Xinyuan-LilyGO/T-Display-S3-Pro/examples/factory/factory.ino

#include <SensorLTR553.hpp>
#include <Wire.h>
#include <WiFi.h>
#include <esp_sntp.h>
#include <XPowersLib.h>
#include "LV_Helper.h"
#include "ui.h"
#include "utilities.h"
#include <esp_camera.h>
#include "ESP32_OV5640_AF.h"
#include "sd_card.h"
#include "EEPROM.h"
/*********************************************************************************
 *                               EEPROM
 *********************************************************************************/
#define EEPROM_SIZE_MAX 5
#define EEPROM_MAGIC_NUM 0xAA
#define EEPROM_FRIST_ADDR  0
#define EEPROM_CAMERA_ADDR 1
uint8_t eeprom_buf[EEPROM_SIZE_MAX];

extern bool camera_rotation_flag;
/*********************************************************************************
 *                              TYPEDEFS
 *********************************************************************************/
static SensorLTR553 als;
static PowersSY6970 PMU;
static WiFiEvent_t event;
static QueueHandle_t wifi_setting_queue;
static EventGroupHandle_t touch_eg;
static bool hasSensor = false, hasPMU = false;
static int autonBrightness = 0;

void eeprom_write(int addr, uint8_t val)
{
    eeprom_buf[EEPROM_FRIST_ADDR] = EEPROM_MAGIC_NUM;
    eeprom_buf[addr] = val;

    for(int i = 0; i < EEPROM_SIZE_MAX; i++){
        EEPROM.write(i, eeprom_buf[i]);
    }
    EEPROM.commit();
    for (int i = 0; i < EEPROM_SIZE_MAX; i++) {
        Serial.print(byte(EEPROM.read(i))); Serial.print(" ");
    }
    Serial.println("");
}

void eeproom_init(void)
{
    if (!EEPROM.begin(EEPROM_SIZE_MAX)) {
        Serial.println("failed to initialise EEPROM"); delay(1000000);
    }
    Serial.println(" bytes read from Flash . Values are:");

    for (int i = 0; i < EEPROM_SIZE_MAX; i++) {
        eeprom_buf[i] = EEPROM.read(i);
        Serial.print(byte(EEPROM.read(i))); Serial.print(" ");
    }

    uint8_t frist_read = eeprom_buf[EEPROM_FRIST_ADDR];
    Serial.printf(" read = %d\n", frist_read);
    if(frist_read == EEPROM_MAGIC_NUM){
        camera_rotation_flag = eeprom_buf[EEPROM_CAMERA_ADDR];
    }else{
        lv_memset_00(eeprom_buf, EEPROM_SIZE_MAX);
        for(int i=0; i < EEPROM_SIZE_MAX; i++){
            EEPROM.write(i, eeprom_buf[i]);
        }
        EEPROM.commit();
    }
}

void lv_auto_brightne_cd(void)
{
    if (!hasSensor)return;
    autonBrightness = autonBrightness == 0 ? 1 : 0;
}

void WiFiEvent(WiFiEvent_t event)
{
    switch (event) {
    case ARDUINO_EVENT_WIFI_READY:
        Serial.println("WiFi interface ready");
        break;
    case ARDUINO_EVENT_WIFI_SCAN_DONE:
        Serial.println("Completed scan for access points");
        break;
    case ARDUINO_EVENT_WIFI_STA_START:
        Serial.println("WiFi client started");
        break;
    case ARDUINO_EVENT_WIFI_STA_STOP:
        Serial.println("WiFi clients stopped");
        break;
    case ARDUINO_EVENT_WIFI_STA_CONNECTED:
        //xQueueSend(wifi_setting_queue, &event, 0);
        Serial.println("Connected to access point");
        break;
    case ARDUINO_EVENT_WIFI_STA_DISCONNECTED:
        xQueueSend(wifi_setting_queue, &event, 0);
        Serial.println("Disconnected from WiFi access point");
        break;
    case ARDUINO_EVENT_WIFI_STA_AUTHMODE_CHANGE:
        Serial.println("Authentication mode of access point has changed");
        break;
    case ARDUINO_EVENT_WIFI_STA_GOT_IP:
        xQueueSend(wifi_setting_queue, &event, 0);
        Serial.print("Obtained IP address: ");
        Serial.println(WiFi.localIP());
        break;
    case ARDUINO_EVENT_WIFI_STA_LOST_IP:
        Serial.println("Lost IP address and IP address is reset to 0");
        break;
    default: break;
    }
}

bool initSensor()
{

    if (!als.begin(Wire, LTR553_SLAVE_ADDRESS, BOARD_I2C_SDA, BOARD_I2C_SCL)) {
        Serial.println("Failed to find LTR553 - check your wiring!");
        return false;
    }

    Serial.println("Init LTR553 Sensor success!");

    // Set the ambient light high and low thresholds.
    // If the value exceeds or falls below the set value, an interrupt will be triggered.
    als.setLightSensorThreshold(10, 200);

    // Set the high and low thresholds of the proximity sensor.
    // If the value exceeds or falls below the set value, an interrupt will be triggered.
    // als.setProximityThreshold(10, 30);

    // Controls the Light Sensor N number of times the measurement data is outside the range
    // defined by the upper and lower threshold limits before asserting the interrupt.
    als.setLightSensorPersists(1);

    // Controls the Proximity  N number of times the measurement data is outside the range
    // defined by the upper and lower threshold limits before asserting the interrupt.
    als.setProximityPersists(1);

    /*
    *  ALS_IRQ_ACTIVE_LOW, // INT pin is considered active when it is a logic 0 (default)
    *  ALS_IRQ_ACTIVE_HIGH // INT pin is considered active when it is a logic 1
    * * */
    als.setIRQLevel(SensorLTR553::ALS_IRQ_ACTIVE_LOW);

    /*
    *  ALS_IRQ_ONLY_PS,    // Only PS measurement can trigger interrupt
    *  ALS_IRQ_ONLY_ALS,   // Only ALS measurement can trigger interrupt
    *  ALS_IRQ_BOTH,       // Both ALS and PS measurement can trigger interrupt
    * * * */
    als.enableIRQ(SensorLTR553::ALS_IRQ_BOTH);

    /*
    *   ALS_GAIN_1X  ,   -> 1 lux to 64k lux (default)
    *   ALS_GAIN_2X  ,   -> 0.5 lux to 32k lux
    *   ALS_GAIN_4X  ,   -> 0.25 lux to 16k lux
    *   ALS_GAIN_8X  ,   -> 0.125 lux to 8k lux
    *   ALS_GAIN_48X ,   -> 0.02 lux to 1.3k lux
    *   ALS_GAIN_96X ,   -> 0.01 lux to 600 lux
    * */
    als.setLightSensorGain(SensorLTR553::ALS_GAIN_1X);

    /*
    *   PS_LED_PLUSE_30KHZ,
    *   PS_LED_PLUSE_40KHZ,
    *   PS_LED_PLUSE_50KHZ,
    *   PS_LED_PLUSE_60KHZ,
    *   PS_LED_PLUSE_70KHZ,
    *   PS_LED_PLUSE_80KHZ,
    *   PS_LED_PLUSE_90KHZ,
    *   PS_LED_PLUSE_100KHZ,
    * * * * * * * * * * */
    als.setPsLedPulsePeriod(SensorLTR553::PS_LED_PLUSE_100KHZ);


    /*
    *   PS_LED_DUTY_25,
    *   PS_LED_DUTY_50,
    *   PS_LED_DUTY_75,
    *   PS_LED_DUTY_100,
    * * * */
    als.setPsLedDutyCycle(SensorLTR553::PS_LED_DUTY_100);


    /*
    *   PS_LED_CUR_5MA,
    *   PS_LED_CUR_10MA,
    *   PS_LED_CUR_20MA,
    *   PS_LED_CUR_50MA,
    *   PS_LED_CUR_100MA,
    * * * * * * * */
    als.setPsLedCurrent(SensorLTR553::PS_LED_CUR_100MA);

    /*
    *   PS_MEAS_RATE_50MS,
    *   PS_MEAS_RATE_70MS,
    *   PS_MEAS_RATE_100MS,
    *   PS_MEAS_RATE_200MS,
    *   PS_MEAS_RATE_500MS,
    *   PS_MEAS_RATE_1000MS,
    *   PS_MEAS_RATE_2000MS,
    *   PS_MEAS_RATE_10MS
    * * * * * * * */
    als.setProximityRate(SensorLTR553::PS_MEAS_RATE_50MS);

    // Number of pulses
    als.setPsLedPulses(1);

    // Enable ambient light sensor
    als.enableLightSensor();

    // Enable proximity sensor
    als.enableProximity();

    // Enable proximity sensor saturation indication
    als.enablePsIndicator();
    return  true;
}

void updatePMU(lv_timer_t *t)
{
    if (!hasPMU)return;
    set_usbAndBattery(PMU.isVbusIn(), PMU.getVbusVoltage(), PMU.getBattVoltage());
}

void updateLightDected(lv_timer_t *t)
{
    int ps_thread = 40; // range: 0 ~ 100
    int ps_time = 2;    // 3 seconds to think there's an object covering the screen
    int ch0, ch1, ps;
    bool saturated = false;
    static uint32_t cnt = 0;
    static bool cover_flag = false;

    if (autonBrightness) {
        Serial.print(" ALS: CH1:"); Serial.print(als.getLightSensor(1));
        Serial.print(" -  CH0:"); Serial.print(als.getLightSensor(0));
        Serial.print(" -  PS:"); Serial.print(als.getProximity(&saturated));
        Serial.print(" -  "); Serial.println(saturated ? "PS saturated" : "PS not saturated");

        if (!hasSensor)
        return;

        ch0 = als.getLightSensor(0);
        ch1 = als.getLightSensor(1);
        ps = als.getProximity(&saturated);

        if(ps > ps_thread){
            if(!cover_flag){
                cnt++;
                if(cnt * t->period > ps_time * 1000){
                    digitalWrite(BOARD_TFT_BL, 0);
                    delay(3);
                    cnt = 0;
                    cover_flag = true;
                }
            }
        } else {
            if(cover_flag){
                cnt++;
                if(cnt * t->period > ps_time * 1000){
                    digitalWrite(BOARD_TFT_BL, 1);
                    delay(3);
                    cnt = 0;
                    cover_flag = false;
                }
            }else{
                cnt = 0;
            }
        }
    }
}

camera_config_t config;
OV5640 ov5640 = OV5640();
void camera_init(void)
{
    config.ledc_channel = LEDC_CHANNEL_0;
    config.ledc_timer = LEDC_TIMER_0;
    config.pin_d0 = CAMERA_PIN_Y2;
    config.pin_d1 = CAMERA_PIN_Y3;
    config.pin_d2 = CAMERA_PIN_Y4;
    config.pin_d3 = CAMERA_PIN_Y5;
    config.pin_d4 = CAMERA_PIN_Y6;
    config.pin_d5 = CAMERA_PIN_Y7;
    config.pin_d6 = CAMERA_PIN_Y8;
    config.pin_d7 = CAMERA_PIN_Y9;
    config.pin_xclk = CAMERA_PIN_XCLK;
    config.pin_pclk = CAMERA_PIN_PCLK;
    config.pin_vsync = CAMERA_PIN_VSYNC;
    config.pin_href = CAMERA_PIN_HREF;
    config.pin_sccb_sda = CAMERA_PIN_SIOD;
    config.pin_sccb_scl = CAMERA_PIN_SIOC;
    config.pin_pwdn = CAMERA_PIN_PWDN;
    config.pin_reset = CAMERA_PIN_RESET;
    config.xclk_freq_hz = XCLK_FREQ_HZ;
#if UI_CAMERA_CANVAS 
    config.pixel_format = PIXFORMAT_RGB565;
    config.frame_size = FRAMESIZE_240X240;
    config.jpeg_quality = 10;
    config.fb_count = 1;
#else
    config.pixel_format = PIXFORMAT_JPEG;
    config.frame_size = FRAMESIZE_HQVGA;
    config.jpeg_quality = 15;
    config.fb_count = 1;
#endif
    config.fb_location = CAMERA_FB_IN_PSRAM;
    config.grab_mode = CAMERA_GRAB_WHEN_EMPTY;

    esp_err_t err = esp_camera_init(&config);
    if (err != ESP_OK) {
        Serial.println("camera init error!");
    }
    sensor_t *s = esp_camera_sensor_get();

    if (s) {
        Serial.print("camera id:");
        Serial.println(s->id.PID);
        camera_sensor_info_t *sinfo = esp_camera_sensor_get_info(&(s->id));
        if (sinfo) {
            Serial.print("camera model:");
            Serial.println(sinfo->name);
        }
        if (s->id.PID == GC0308_PID) {
            s->set_vflip(s, 0); // This can't flip the picture vertically. Watch out!
            s->set_hmirror(s, 0);
        }else if (s->id.PID == OV5640_PID){
            ov5640.start(s);
            if (ov5640.focusInit() == 0) {
                Serial.println("OV5640_Focus_Init Successful!");
            }

            if (ov5640.autoFocusMode() == 0) {
                Serial.println("OV5640_Auto_Focus Successful!");
            }
            s->set_vflip(s, 1);
            s->set_hmirror(s, 0);
        }
    }

    // Initialize Camera LED
    // Adjust the LED duty cycle to save power and heat.
    // If you directly set the LED to HIGH, the heat brought by the LED will be huge,
    // and the current consumption will also be huge.
    ledcSetup(LEDC_WHITE_CH, 1000, 8);
    ledcAttachPin(CAMERA_WHITH_LED, LEDC_WHITE_CH);
    ledcWrite(LEDC_WHITE_CH, 0);
    // ledcWrite(LEDC_WHITE_CH, 20);
}


void setup()
{
    touch_eg = xEventGroupCreate();
    wifi_setting_queue = xQueueCreate(5, sizeof(uint16_t));

    Serial.begin(115200);

    eeproom_init();

    // vibrating motor init
    pinMode(VIBRATING_MOTOR, OUTPUT);
    digitalWrite(VIBRATING_MOTOR, LOW);

    WiFi.disconnect(true);
    WiFi.onEvent(WiFiEvent);

    const char *ntpServer1 = "pool.ntp.org";
    const char *ntpServer2 = "time.nist.gov";
    const char *tz  = "CST-8";                  //timezone
    configTzTime(tz, ntpServer1, ntpServer2);

    camera_init();

    hasPMU =  PMU.init(Wire, BOARD_I2C_SDA, BOARD_I2C_SCL, SY6970_SLAVE_ADDRESS);
    if (!hasPMU) {
        Serial.println("PMU is not online...");
    } else {
        PMU.disableOTG();
        PMU.enableADCMeasure();
        PMU.enableCharge();
    }

    hasSensor = initSensor();

    lv_helper();

    sd_card_init();

    lv_touch_homekey_set_cb(return_home_cd);

    ui_init();

    lv_timer_create(updatePMU, 1000, NULL);

    // TODO:
    lv_timer_create(updateLightDected, 500, NULL);
}

void loop()
{
    if (xQueueReceive(wifi_setting_queue, &event, 0)) {
        if (event == ARDUINO_EVENT_WIFI_STA_GOT_IP
                || event == ARDUINO_EVENT_WIFI_STA_DISCONNECTED) {
            wifi_connect_cd();
        }
    }
    lv_task_handler();
    delay(2);

}
