Xinyuan-LilyGO/T-Display-S3-Pro/examples/BHI260AP_Sensor/BHI260AP_Sensor.ino

/**
 *
 * @license MIT License
 *
 * Copyright (c) 2023 lewis he
 *
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
 * @file      BHI260AP_6DoF.ino
 * @author    Lewis He (lewishe@outlook.com)
 * @date      2023-09-06
 * @note      Changed from Boschsensortec API https://github.com/boschsensortec/BHY2_SensorAPI
 */
#include <Wire.h>
#include <SPI.h>
#include <Arduino.h>
#include "SensorBHI260AP.hpp"

#define SENSOR_SDA                  5
#define SENSOR_SCL                  6
#define SENSOR_IRQ                  21
#define SENSOR_RST                  -1

SensorBHI260AP bhy;

void accel_process_callback(uint8_t sensor_id, uint8_t *data_ptr, uint32_t len, uint64_t *timestamp)
{
    struct bhy2_data_xyz data;
    float scaling_factor = get_sensor_default_scaling(sensor_id);
    bhy2_parse_xyz(data_ptr, &data);
    Serial.print(bhy.getSensorName(sensor_id));
    Serial.print(":");
    Serial.printf("x: %f, y: %f, z: %f;\r\n",
                  data.x * scaling_factor,
                  data.y * scaling_factor,
                  data.z * scaling_factor
                 );
}


void gyro_process_callback(uint8_t sensor_id, uint8_t *data_ptr, uint32_t len, uint64_t *timestamp)
{
    struct bhy2_data_xyz data;
    float scaling_factor = get_sensor_default_scaling(sensor_id);
    bhy2_parse_xyz(data_ptr, &data);
    Serial.print(bhy.getSensorName(sensor_id));
    Serial.print(":");
    Serial.printf("x: %f, y: %f, z: %f;\r\n",
                  data.x * scaling_factor,
                  data.y * scaling_factor,
                  data.z * scaling_factor
                 );
}

void setup()
{
    Serial.begin(115200);
    while (!Serial);

    // Set the reset pin and interrupt pin, if any
    bhy.setPins(SENSOR_RST, SENSOR_IRQ);

    Serial.println("Initializing Sensors...");
    // Using I2C interface
    if (!bhy.init(Wire, SENSOR_SDA, SENSOR_SCL, BHI260AP_SLAVE_ADDRESS_L)) {
        Serial.print("Failed to initialize sensor - error code:");
        Serial.println(bhy.getError());
        while (1) {
            delay(1000);
        }
    }

    Serial.println("Initializing the sensor successfully!");

    // Output all available sensors to Serial
    bhy.printSensors(Serial);

    float sample_rate = 100.0;      /* Read out hintr_ctrl measured at 100Hz */
    uint32_t report_latency_ms = 0; /* Report immediately */

    // Enable acceleration
    bhy.configure(SENSOR_ID_ACC_PASS, sample_rate, report_latency_ms);
    // Enable gyroscope
    bhy.configure(SENSOR_ID_GYRO_PASS, sample_rate, report_latency_ms);

    // Set the acceleration sensor result callback function
    bhy.onResultEvent(SENSOR_ID_ACC_PASS, accel_process_callback);

    // Set the gyroscope sensor result callback function
    bhy.onResultEvent(SENSOR_ID_GYRO_PASS, gyro_process_callback);

}


void loop()
{
    // Update sensor fifo
    bhy.update();
    delay(50);
}
