Xinyuan-LilyGO/T-Display-S3-Pro/examples/PMU_Example/PMU_Example.ino

/**
 * @file      PMU_Example.ino
 * @author    Lewis He (lewishe@outlook.com)
 * @license   MIT
 * @copyright Copyright (c) 2023  Shenzhen Xin Yuan Electronic Technology Co., Ltd
 * @date      2023-09-25
 * @note      USB_CDC_ON_BOOT = Disable  , Messages are output from the QWIIC serial port
 */
#include <XPowersLib.h>
#include "utilities.h"


PowersSY6970 PMU;

uint32_t cycleInterval;

void setup()
{
    Serial.begin(115200);

    bool result = PMU.init(Wire, BOARD_I2C_SDA, BOARD_I2C_SCL, SY6970_SLAVE_ADDRESS);

    if (result == false) {
        while (1) {
            Serial.println("PMU is not online...");
            delay(50);
        }
    }
    // Set USB input current limit
    PMU.setInputCurrentLimit(1000);

    // The onboard battery is fully charged at 4.35V
    // Set the charging target voltage, Range:3840 ~ 4608mV ,step:16 mV
    PMU.setChargeTargetVoltage(4352);

    // Set the precharge current , Range: 64mA ~ 1024mA ,step:64mA
    PMU.setPrechargeCurr(64);

    // Set the charging current , Range:0~5056mA ,step:64mA
    PMU.setChargerConstantCurr(320);

    // When the battery is not connected and the USB is plugged in, the board's LED status indicator light will flash.
    // You can use `PMU.disableStatLed();` to turn off the indicator light,
    // but this means that if the battery is connected for charging, the LED light will also be disabled.
    // PMU.disableStatLed();

    // Enable charging led
    PMU.enableStatLed();

    // To obtain voltage data, the ADC must be enabled first
    PMU.enableADCMeasure();


    // For devices that have been connected to the battery, the charging function is turned on by default.
    // PMU.enableCharge();

    // For boards without an external battery, the charging function should be turned off, otherwise the power supply current of the power chip will be limited.
    PMU.disableCharge();

}



void loop()
{

    // SY6970 When VBUS is input, the battery voltage detection will not take effect
    if (millis() > cycleInterval) {

        Serial.println("Sats        VBUS    VBAT   SYS    VbusStatus      String   ChargeStatus     String      TargetVoltage       ChargeCurrent       Precharge       NTCStatus           String");
        Serial.println("            (mV)    (mV)   (mV)   (HEX)                         (HEX)                    (mV)                 (mA)                   (mA)           (HEX)           ");
        Serial.println("--------------------------------------------------------------------------------------------------------------------------------");
        Serial.print(PMU.isVbusIn() ? "Connected" : "Disconnect"); Serial.print("\t");
        Serial.print(PMU.getVbusVoltage()); Serial.print("\t");
        Serial.print(PMU.getBattVoltage()); Serial.print("\t");
        Serial.print(PMU.getSystemVoltage()); Serial.print("\t");
        Serial.print("0x");
        Serial.print(PMU.getBusStatus(), HEX); Serial.print("\t");
        Serial.print(PMU.getBusStatusString()); Serial.print("\t");
        Serial.print("0x");
        Serial.print(PMU.chargeStatus(), HEX); Serial.print("\t");
        Serial.print(PMU.getChargeStatusString()); Serial.print("\t");

        Serial.print(PMU.getChargeTargetVoltage()); Serial.print("\t");
        Serial.print(PMU.getChargerConstantCurr()); Serial.print("\t");
        Serial.print(PMU.getPrechargeCurr()); Serial.print("\t");
        Serial.print(PMU.getNTCStatus()); Serial.print("\t");
        Serial.print(PMU.getNTCStatusString()); Serial.print("\t");

        Serial.println();
        Serial.println();

        cycleInterval = millis() + 1000;
    }

}
