Xinyuan-LilyGO/T-Display-S3-Pro/examples/ICM20948/ICM20948.ino

/***************************************************************************
* Example sketch for the ICM20948_WE library
*
* This sketch shows how to setup the gyroscope and how to query gyroscope
* related data. 
* 
* Further information can be found on:
*
* https://wolles-elektronikkiste.de/icm-20948-9-achsensensor-teil-i (German)
* https://wolles-elektronikkiste.de/en/icm-20948-9-axis-sensor-part-i (English)
* 
***************************************************************************/

#include "ui.h"
#include <Wire.h>
#include <ICM20948_WE.h>
#define ICM20948_ADDR 0x68

bool imu_icm20948_init = false;

/* There are several ways to create your ICM20948 object:
 * ICM20948_WE myIMU = ICM20948_WE()              -> uses Wire / I2C Address = 0x68
 * ICM20948_WE myIMU = ICM20948_WE(ICM20948_ADDR) -> uses Wire / ICM20948_ADDR
 * ICM20948_WE myIMU = ICM20948_WE(&wire2)        -> uses the TwoWire object wire2 / ICM20948_ADDR
 * ICM20948_WE myIMU = ICM20948_WE(&wire2, ICM20948_ADDR) -> all together
 * ICM20948_WE myIMU = ICM20948_WE(CS_PIN, spi);  -> uses SPI, spi is just a flag, see SPI example
 * ICM20948_WE myIMU = ICM20948_WE(&SPI, CS_PIN, spi);  -> uses SPI / passes the SPI object, spi is just a flag, see SPI example
 */
ICM20948_WE myIMU = ICM20948_WE(ICM20948_ADDR);

void setup() {
  Wire.begin(5, 6);
  Serial.begin(115200);
//   while(!Serial) {}

  imu_icm20948_init = myIMU.init();
  
  if(imu_icm20948_init){
      Serial.println("ICM20948 is connected");
  }
  else{
    Serial.println("ICM20948 does not respond");
  }

  Serial.println("Position your ICM20948 flat and don't move it - calibrating...");
  delay(1000);
  myIMU.autoOffsets();
  Serial.println("Done!"); 
  
  /*  The gyroscope data is not zero, even if you don't move the ICM20948. 
   *  To start at zero, you can apply offset values. These are the gyroscope raw values you obtain
   *  using the +/- 250 degrees/s range. 
   *  Use either autoOffsets or setGyrOffsets, not both.
   */
  //myIMU.setGyrOffsets(-115.0, 130.0, 105.0);
  
  /* enables or disables the gyroscope sensor, default: enabled */
  // myIMU.enableGyr(false);

  /*  ICM20948_GYRO_RANGE_250       250 degrees per second (default)
   *  ICM20948_GYRO_RANGE_500       500 degrees per second
   *  ICM20948_GYRO_RANGE_1000     1000 degrees per second
   *  ICM20948_GYRO_RANGE_2000     2000 degrees per second
   */
  myIMU.setGyrRange(ICM20948_GYRO_RANGE_250);
  
  /*  Choose a level for the Digital Low Pass Filter or switch it off. 
   *  ICM20948_DLPF_0, ICM20948_DLPF_2, ...... ICM20948_DLPF_7, ICM20948_DLPF_OFF 
   *  
   *  DLPF       3dB Bandwidth [Hz]      Output Rate [Hz]
   *    0              196.6               1125/(1+GSRD) 
   *    1              151.8               1125/(1+GSRD)
   *    2              119.5               1125/(1+GSRD)
   *    3               51.2               1125/(1+GSRD)
   *    4               23.9               1125/(1+GSRD)
   *    5               11.6               1125/(1+GSRD)
   *    6                5.7               1125/(1+GSRD) 
   *    7              361.4               1125/(1+GSRD)
   *    OFF          12106.0               9000
   *    
   *    GSRD = Gyroscope Sample Rate Divider (0...255)
   *    You achieve lowest noise using level 6  
   */
  myIMU.setGyrDLPF(ICM20948_DLPF_6);  
  
  /*  Gyroscope sample rate divider divides the output rate of the gyroscope.
   *  Sample rate = Basic sample rate / (1 + divider) 
   *  It can only be applied if the corresponding DLPF is not OFF!
   *  Divider is a number 0...255
   *  If sample rates are set for the accelerometer and the gyroscope, the gyroscope
   *  sample rate has priority.
   */
  //myIMU.setGyrSampleRateDivider(10);

    if (!myIMU.initMagnetometer()) {
        Serial.println("Magnetometer does not respond");
    }
    else {
        Serial.println("Magnetometer is connected");
    }
    myIMU.setMagOpMode(AK09916_CONT_MODE_20HZ);


    ui_init(SCR_ROTATION_270);
    if(imu_icm20948_init){
        ui_enter();
    } else{
        lv_obj_t * label1 = lv_label_create(lv_scr_act());
        lv_label_set_long_mode(label1, LV_LABEL_LONG_WRAP);     /*Break the long lines*/
        lv_label_set_recolor(label1, true);                      /*Enable re-coloring by commands in the text*/
        lv_label_set_text(label1, "#ff0000 error:# Failed to initialize the 9-axis sensor. Please check the I2C wiring"
                        " and make sure the device has a 9-axis sensor.");
        lv_obj_set_width(label1, 400);  /*Set smaller width to make the lines wrap*/
        lv_obj_set_style_text_align(label1, LV_TEXT_ALIGN_CENTER, 0);
        lv_obj_align(label1, LV_ALIGN_CENTER, 0, 0);
    }
}

void loop() {
    lv_task_handler();
    delay(2);
}
