Xinyuan-LilyGO/T-Display-S3-Pro/examples/IIC_Scan_2/IIC_Scan_2.ino

/*
 * @Description: IIC_Scan_2
 * @Author: LILYGO_L
 * @Date: 2023-12-26 14:59:18
 * @LastEditTime: 2024-05-07 14:39:18
 * @License: GPL 3.0
 */
#include <Arduino.h>
#include <Wire.h>
#include "pin_config.h"

#define SDA IIC_SDA
#define SCL IIC_SCL

void scan_i2c_device(TwoWire &i2c)
{
    Serial.println("Scanning for I2C devices ...");
    Serial.print("      ");
    for (int i = 0; i < 0x10; i++)
    {
        Serial.printf("0x%02X|", i);
    }
    uint8_t error;
    for (int j = 0; j < 0x80; j += 0x10)
    {
        Serial.println();
        Serial.printf("0x%02X |", j);
        for (int i = 0; i < 0x10; i++)
        {
            Wire.beginTransmission(i | j);
            error = Wire.endTransmission();
            if (error == 0)
                Serial.printf("0x%02X|", i | j);
            else
                Serial.print(" -- |");
        }
    }
    Serial.println();
}

void setup()
{
    Serial.begin(115200);
    Serial.println("Ciallo");

    pinMode(RT9080_EN, OUTPUT);
    digitalWrite(RT9080_EN, HIGH);

    Wire.begin(SDA, SCL);
}

void loop()
{
    scan_i2c_device(Wire);
    delay(1000);
}
