Xinyuan-LilyGO/T-Display-S3-Pro/examples/Cellphone/src/ui_img_camera_png.c

// LVGL version: 8.3.5
// Project name: phoneui

#include "Arduino.h"
#include "lvgl.h"

#ifndef LV_ATTRIBUTE_MEM_ALIGN
    #define LV_ATTRIBUTE_MEM_ALIGN
#endif

// IMAGE DATA: assets\camera.png
const LV_ATTRIBUTE_MEM_ALIGN uint8_t ui_img_camera_png_data[] = {
    0xB5,0xD7,0x00,0xB5,0xD7,0x00,0xB5,0xB7,0x00,0xC6,0x18,0x00,0xD6,0xBA,0x00,0xD6,0xBA,0x00,0xBD,0xF8,0x00,0xBD,0xF7,0x00,0xDE,0xFB,0x32,0xDE,0xDB,0x6E,0xDE,0xDB,0xA1,0xE7,0x1C,0xC5,0xDE,0xDB,0xD6,0xE7,0x1C,0xE4,0xE7,0x1C,0xE8,0xE7,0x1C,0xEB,0xE7,0x1C,0xEF,0xE7,0x1C,0xEE,0xE7,0x1C,0xEE,0xE7,0x1C,0xEE,0xE7,0x1C,0xEE,0xE7,0x1C,0xEE,0xE7,0x1C,0xEE,0xE7,0x1C,0xEE,0xE7,0x1C,0xEE,0xE7,0x1C,0xEE,0xE7,0x1C,0xEE,0xE7,0x1C,0xEE,0xE7,0x1C,0xEE,0xE7,0x1C,0xEE,0xE7,0x1C,0xEE,0xE7,0x1C,0xEE,0xE7,0x1C,0xEE,0xE7,0x1C,0xEE,0xE7,0x1C,0xEE,0xE7,0x1C,0xEE,0xE7,0x1C,0xEE,0xE7,0x1C,0xEE,0xE7,0x1C,0xEE,0xE7,0x1C,0xEE,0xE7,0x1C,0xEE,0xE7,0x1C,0xEB,0xE7,0x1C,0xE9,0xE7,0x1C,0xE3,0xDE,0xFB,0xD6,0xE7,0x1C,0xC5,0xD6,0xBA,0xA3,0xD6,0xBA,0x71,0xDE,0xFC,0x33,0xBD,0xF8,0x00,0xB5,0xB7,0x00,0xD6,0x9A,0x00,0xC6,0x59,0x00,0xB5,0xB7,0x00,0xB5,0xD7,0x00,0xB5,0xD7,0x00,0xB5,0xD7,0x00,0xB5,0xD7,0x00,0xB5,0xD7,0x00,0xB5,0xB7,0x00,0xC6,0x18,0x00,0xD6,0xBA,0x00,0xCE,0x7A,0x00,0xCE,0x79,0x50,
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
};
const lv_img_dsc_t ui_img_camera_png = {
    .header.always_zero = 0,
    .header.w = 57,
    .header.h = 57,
    .data_size = sizeof(ui_img_camera_png_data),
    .header.cf = LV_IMG_CF_TRUE_COLOR_ALPHA,
    .data = ui_img_camera_png_data
};
